ADDTDR/TinyNumberHat/images/IMG_4520.jpeg

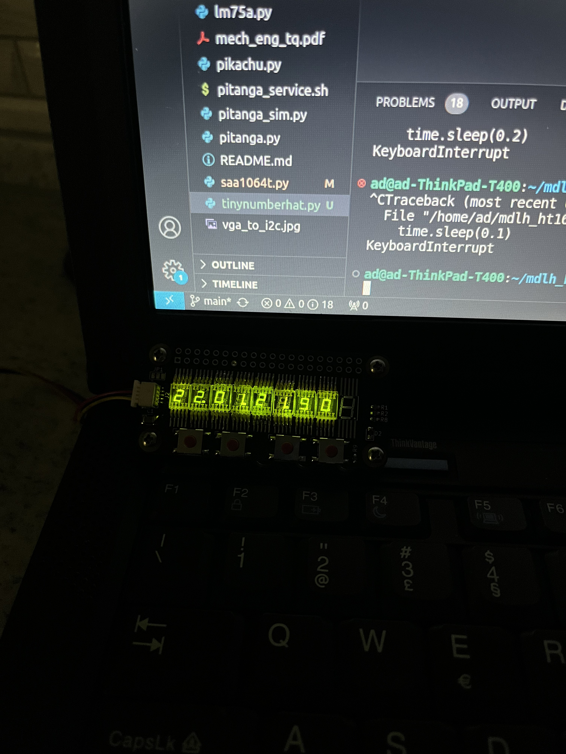
images/IMG_4520.jpeg
