ADDTDR/TinyNumberHat/images/IMG_4530 2.jpeg

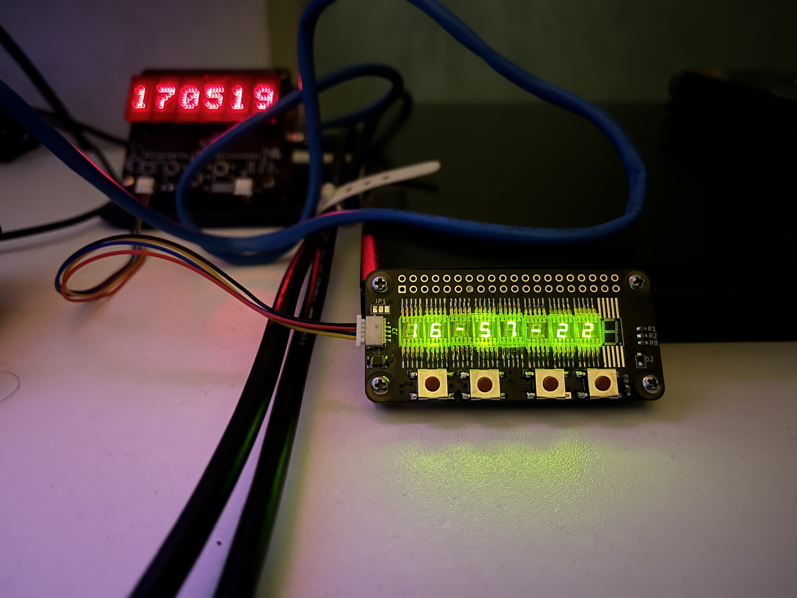
images/IMG_4530 2.jpeg
