ADDTDR/TinyNumberHat/images/IMG_6323.jpeg

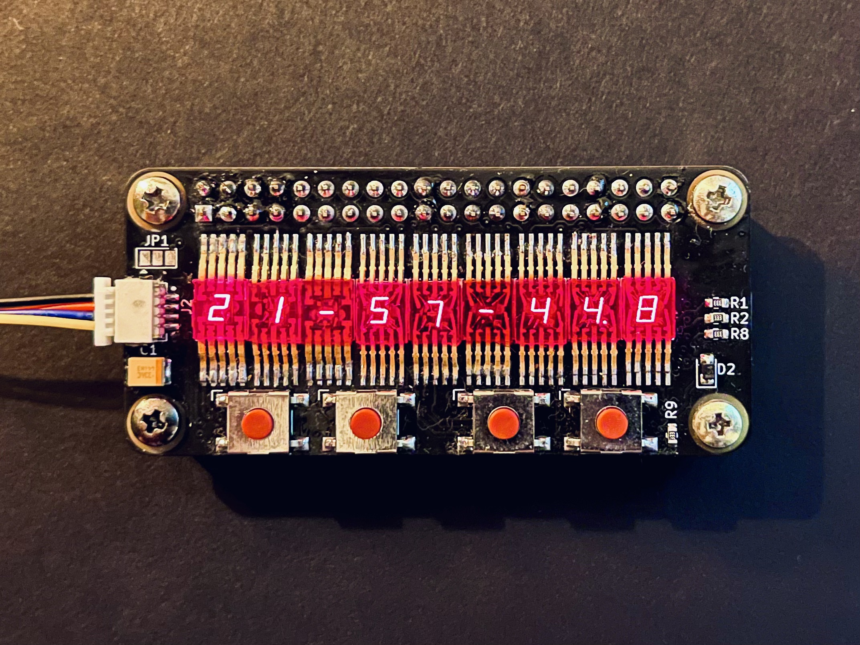
images/IMG_6323.jpeg
