ADDTDR/TinyNumberHat/images/IMG_6324.jpeg

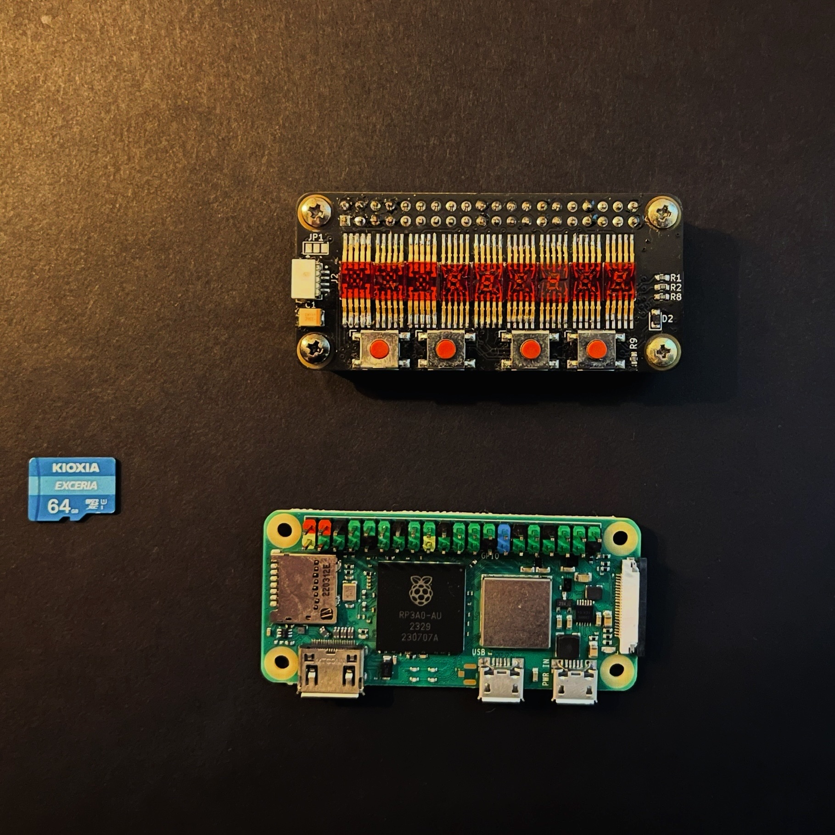
images/IMG_6324.jpeg
