ADDTDR/TinyNumberHat/images/IMG_6325.jpeg

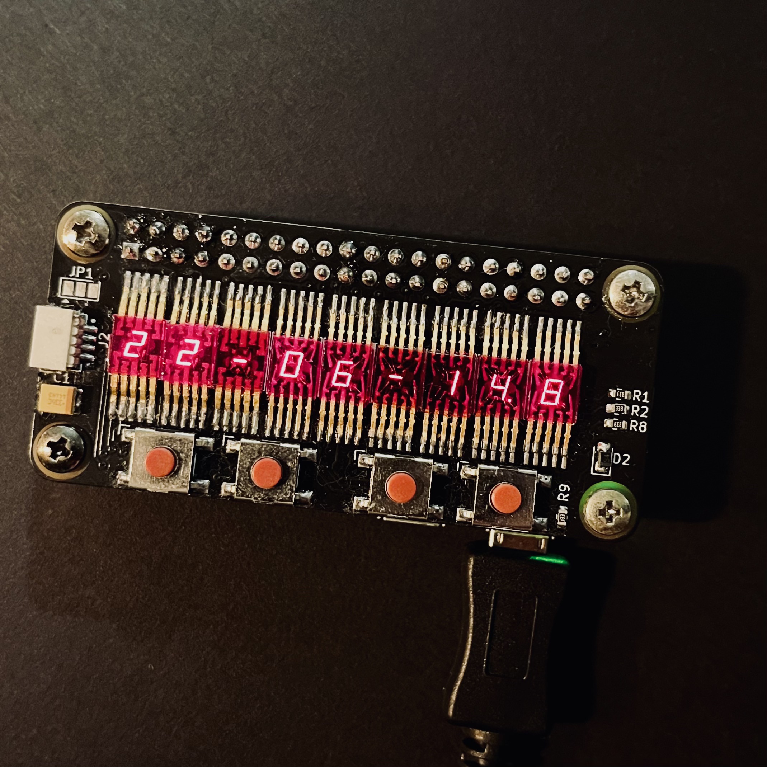
images/IMG_6325.jpeg
