ADDTDR/TinyNumberHat/images/IMG_6326.jpeg

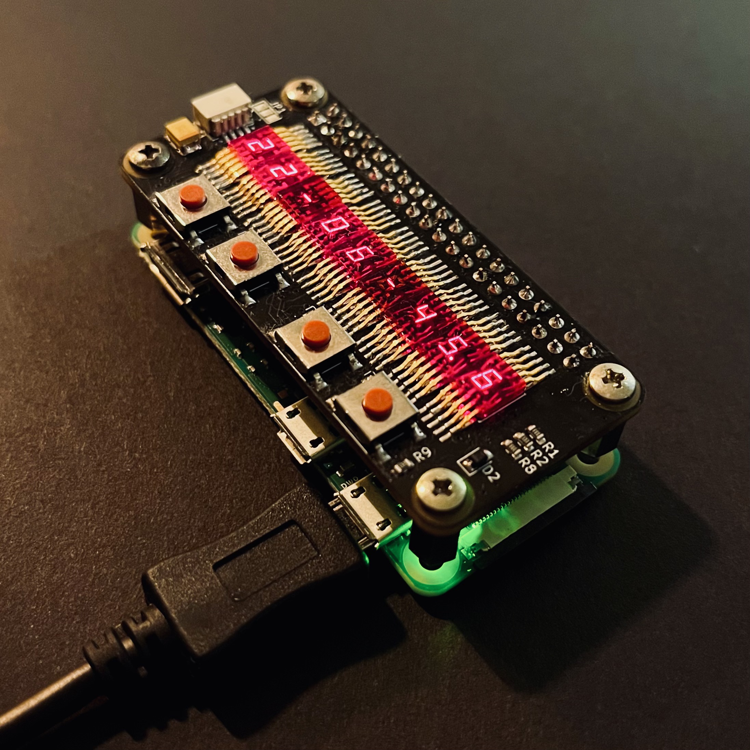
images/IMG_6326.jpeg
