ADDTDR/TinyNumberHat/Software/ArduinoSTM32G0F6X_GPS_CLOCK/Conection.PNG

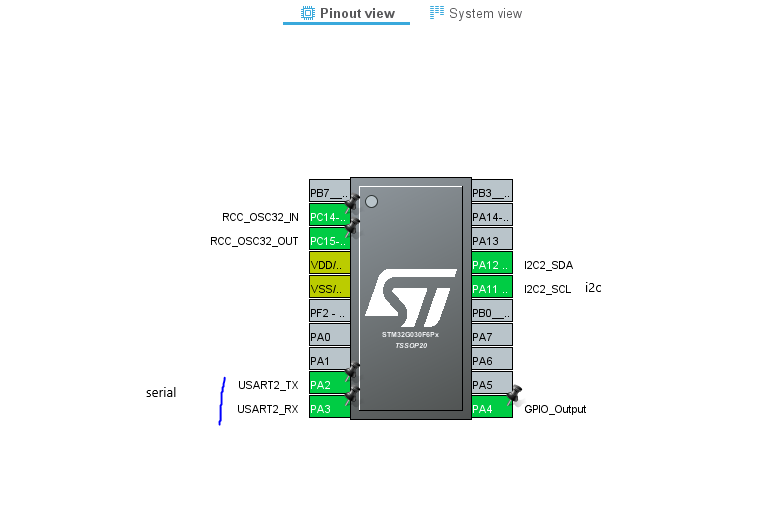
Software/ArduinoSTM32G0F6X_GPS_CLOCK/Conection.PNG
