ADDTDR/TinyNumberHat/images/IMG_4519.jpeg

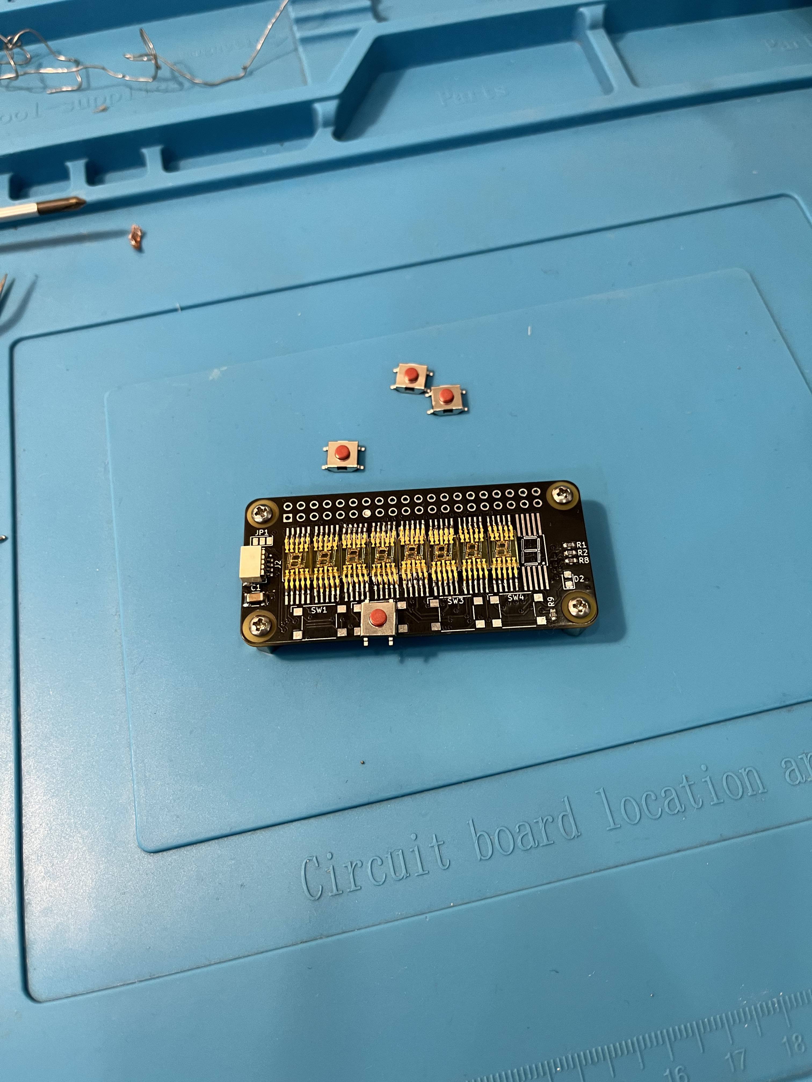
images/IMG_4519.jpeg
