ADDTDR/TinyNumberHat/images/IMG_4539.jpeg

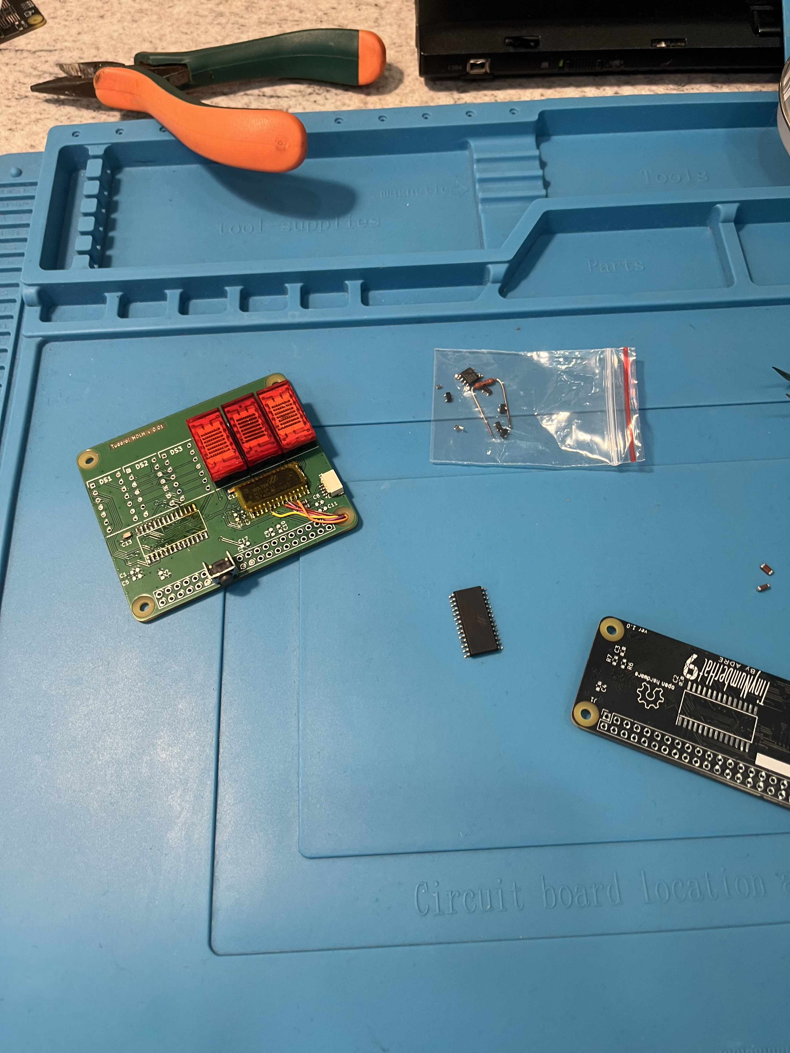
images/IMG_4539.jpeg
